MekhyW/KSP-Controller/firmware/src/backlit-buttons.h

#define BUT_PIO      PIOA
#define BUT_PIO_ID   ID_PIOA
#define BUT_IDX      11
#define BUT_IDX_MASK (1 << BUT_IDX) 
#define BUT1_PIO      PIOC
#define BUT1_PIO_ID   ID_PIOC
#define BUT1_IDX      31
#define BUT1_IDX_MASK (1 << BUT1_IDX)
#define BUT2_PIO      PIOB
#define BUT2_PIO_ID   ID_PIOB
#define BUT2_IDX      3
#define BUT2_IDX_MASK (1 << BUT2_IDX)
#define BUT3_PIO      PIOA
#define BUT3_PIO_ID   ID_PIOA
#define BUT3_IDX      0
#define BUT3_IDX_MASK (1 << BUT3_IDX)
#define BUT4_PIO      PIOD
#define BUT4_PIO_ID   ID_PIOD
#define BUT4_IDX      28
#define BUT4_IDX_MASK (1 << BUT4_IDX)
#define BUT5_PIO      PIOA
#define BUT5_PIO_ID   ID_PIOA
#define BUT5_IDX      4
#define BUT5_IDX_MASK (1 << BUT5_IDX)
#define BUT6_PIO      PIOD
#define BUT6_PIO_ID   ID_PIOD
#define BUT6_IDX      25
#define BUT6_IDX_MASK (1 << BUT6_IDX)
#define BUT7_PIO      PIOA
#define BUT7_PIO_ID   ID_PIOA
#define BUT7_IDX      19
#define BUT7_IDX_MASK (1 << BUT7_IDX)
#define BUT8_PIO      PIOB
#define BUT8_PIO_ID   ID_PIOB
#define BUT8_IDX      2
#define BUT8_IDX_MASK (1 << BUT8_IDX)
#define BUT9_PIO      PIOC
#define BUT9_PIO_ID   ID_PIOC
#define BUT9_IDX      30
#define BUT9_IDX_MASK (1 << BUT9_IDX)
#define BUT10_PIO      PIOC
#define BUT10_PIO_ID   ID_PIOC
#define BUT10_IDX      17
#define BUT10_IDX_MASK (1 << BUT10_IDX)

#define LED_PIO      PIOC
#define LED_PIO_ID   ID_PIOC
#define LED_IDX      8
#define LED_IDX_MASK (1 << LED_IDX)

#define LED1_PIO      PIOA
#define LED1_PIO_ID   ID_PIOA
#define LED1_IDX      6
#define LED1_IDX_MASK (1 << LED1_IDX)

#define LED2_PIO      PIOC
#define LED2_PIO_ID   ID_PIOC
#define LED2_IDX      19
#define LED2_IDX_MASK (1 << LED2_IDX)

#define LED3_PIO      PIOA
#define LED3_PIO_ID   ID_PIOA
#define LED3_IDX      2
#define LED3_IDX_MASK (1 << LED3_IDX)

#define LED4_PIO      PIOA
#define LED4_PIO_ID   ID_PIOA
#define LED4_IDX      3
#define LED4_IDX_MASK (1 << LED4_IDX)

#define LED5_PIO      PIOA
#define LED5_PIO_ID   ID_PIOA
#define LED5_IDX      27
#define LED5_IDX_MASK (1 << LED5_IDX)

#define LED6_PIO      PIOC
#define LED6_PIO_ID   ID_PIOC
#define LED6_IDX      13
#define LED6_IDX_MASK (1 << LED6_IDX)

#define LED7_PIO      PIOD
#define LED7_PIO_ID   ID_PIOD
#define LED7_IDX      11
#define LED7_IDX_MASK (1 << LED7_IDX)

#define LED8_PIO      PIOD
#define LED8_PIO_ID   ID_PIOD
#define LED8_IDX      26
#define LED8_IDX_MASK (1 << LED8_IDX)

#define LED9_PIO      PIOA
#define LED9_PIO_ID   ID_PIOA
#define LED9_IDX      24
#define LED9_IDX_MASK (1 << LED9_IDX)

#define LED10_PIO      PIOD
#define LED10_PIO_ID   ID_PIOD
#define LED10_IDX      22
#define LED10_IDX_MASK (1 << LED10_IDX)

#define LED11_PIO      PIOD
#define LED11_PIO_ID   ID_PIOD
#define LED11_IDX      20
#define LED11_IDX_MASK (1 << LED11_IDX)

#define LED12_PIO      PIOA
#define LED12_PIO_ID   ID_PIOA
#define LED12_IDX      13
#define LED12_IDX_MASK (1 << LED12_IDX)
