MekhyW/KSP-Controller/firmware/src/abort.h

#define ABORT_PIO      PIOD
#define ABORT_PIO_ID   ID_PIOD
#define ABORT_IDX      31
#define ABORT_IDX_MASK (1 << ABORT_IDX)

#define LED_ABORT_PIO      PIOA
#define LED_ABORT_PIO_ID   ID_PIOA
#define LED_ABORT_IDX      9
#define LED_ABORT_IDX_MASK (1 << LED_ABORT_IDX)
